IdleHandsProject/gb_walkie_talkie/CAD/images/2018-09-30_20-19-31.png

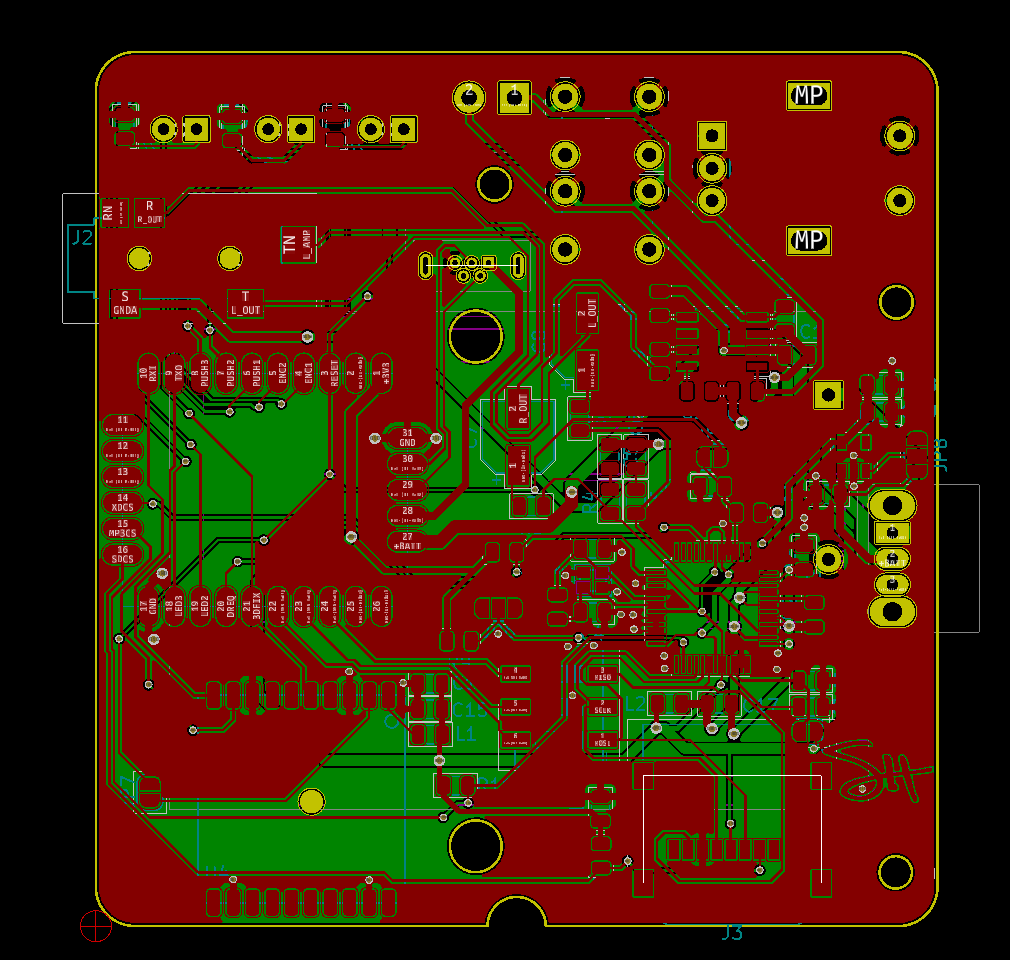
CAD/images/2018-09-30_20-19-31.png
