IdleHandsProject/gb_walkie_talkie/CAD/STP/tactileswitch-long.STEP

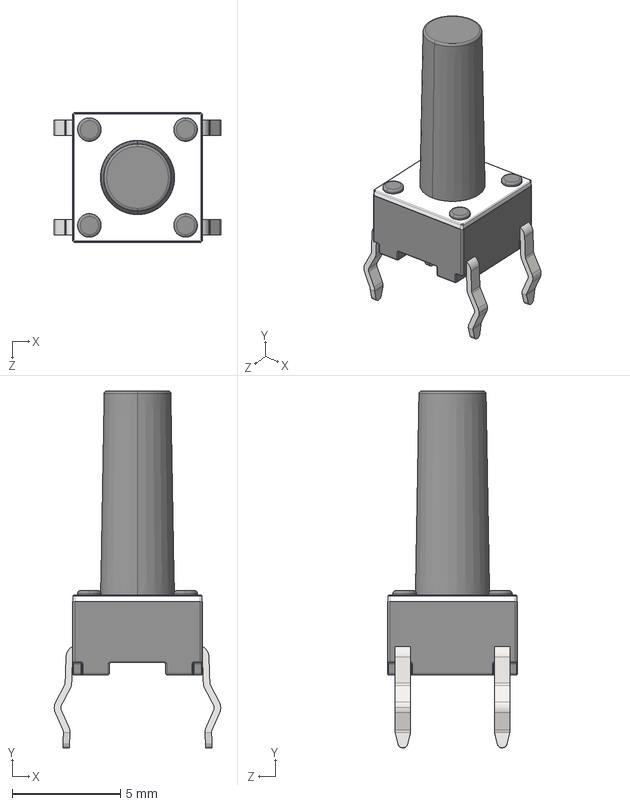
[picture p19: CAD file, 2018-10-15]
CAD/STP/tactileswitch-long.STEP
7.69 x 16.5 x 6.01 mm
