IdleHandsProject/gb_walkie_talkie/CAD/STP/micro SD Card Slot.step

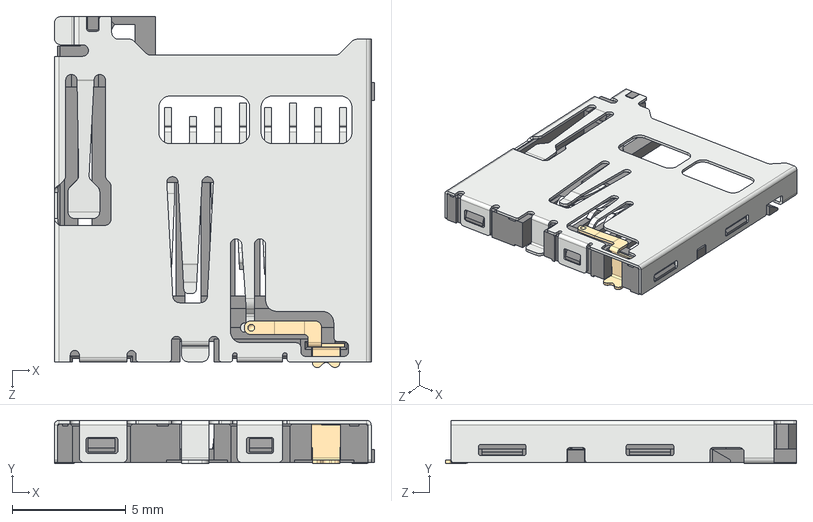
[picture p20: CAD file, 2018-10-15]
CAD/STP/micro SD Card Slot.step
14.1 x 1.90 x 15.5 mm
microSD_Body
microSD_Cover
microSD_Card_Detect
microSD_Pin_11.15 x 5
microSD_Pin_11.35 x 2
microSD_Pin_10.75
