IdleHandsProject/gb_walkie_talkie/CAD/STP/BC4AAW.STEP

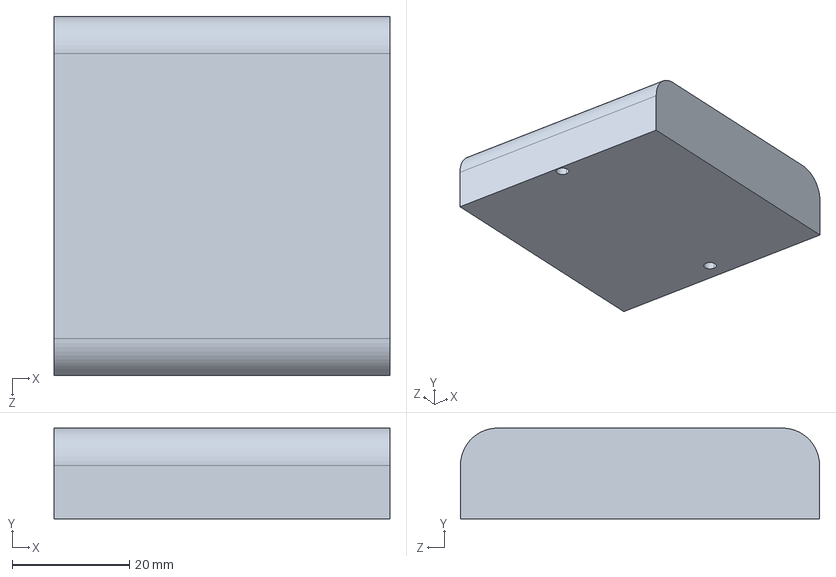
[picture p21: CAD file, 2018-10-15]
CAD/STP/BC4AAW.STEP
57.3 x 15.5 x 61.2 mm
