IdleHandsProject/gb_walkie_talkie/CAD/STP/BH3AAPC.STEP

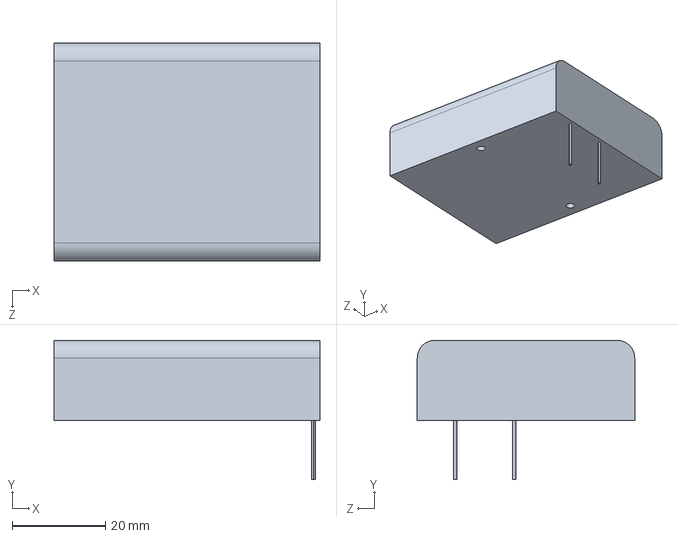
[picture p22: CAD file, 2018-10-15]
CAD/STP/BH3AAPC.STEP
57.1 x 29.9 x 46.7 mm
